GerritMihu/htl-loetregler-mini/3d/griffstück/griffstück_unten_v0.0.4.stl

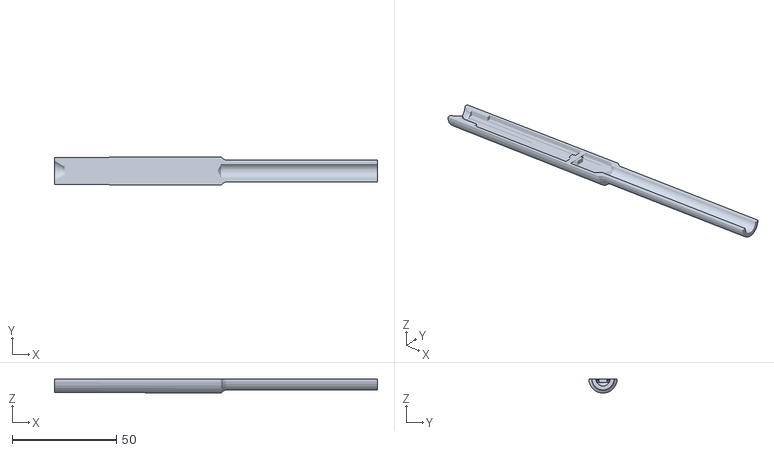
[picture p18: CAD file, 2024-12-23]
3d/griffstück/griffstück_unten_v0.0.4.stl
155.0 x 13.6 x 6.75
