GerritMihu/htl-loetregler-mini/3d/griffstück/griffstück_halbschale-rund_v2_Polycarbonat.3mf

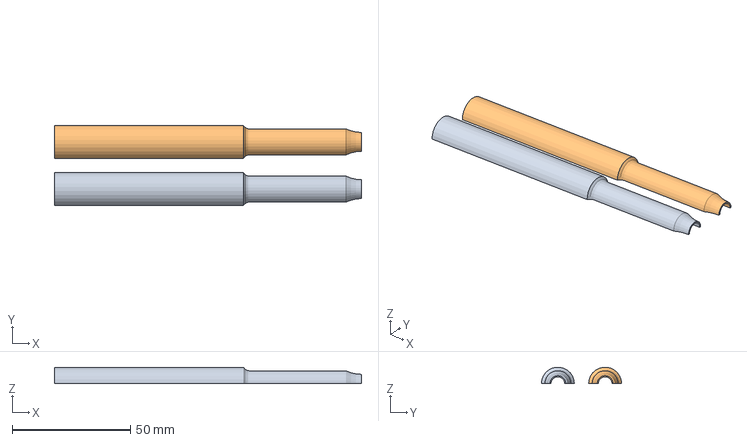
[picture p19: CAD file, 2024-12-23]
3d/griffstück/griffstück_halbschale-rund_v2_Polycarbonat.3mf
130.0 x 34.0 x 6.95 mm
