GerritMihu/htl-loetregler-mini/3d/griffstück/griffstück_v2_komplettset.3mf

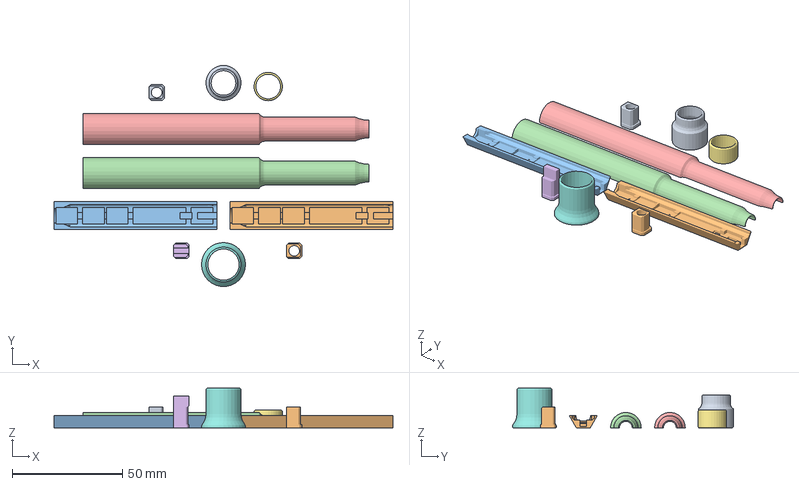
[picture p20: CAD file, 2024-12-23]
3d/griffstück/griffstück_v2_komplettset.3mf
154.0 x 100.5 x 18.0 mm
mittenring_v2.1.stl
griffstück_halbschale-hex_v2.stl
griffstück_halbschale-rund_v2.stl
griffstück_isolator_tc+.stl
endring_v2.1.stl
fingerkuppenring_v2.2.stl
griffstück_isolator_htc-_h+.stl
