GerritMihu/htl-loetregler-mini/3d/griffstück/griffstück_isolator_htc-_h+.stl

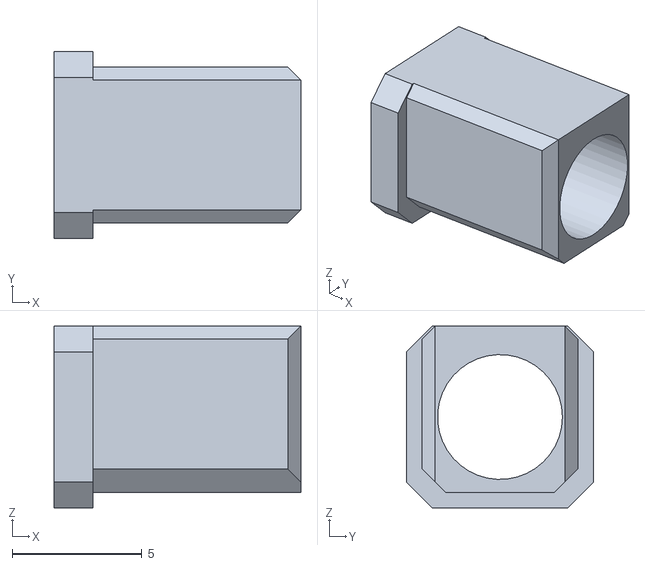
[picture p21: CAD file, 2024-12-23]
3d/griffstück/griffstück_isolator_htc-_h+.stl
9.50 x 7.20 x 7.00
