GerritMihu/htl-loetregler-mini/3d/griffstück/griffstück_oben_v0.0.1.3mf

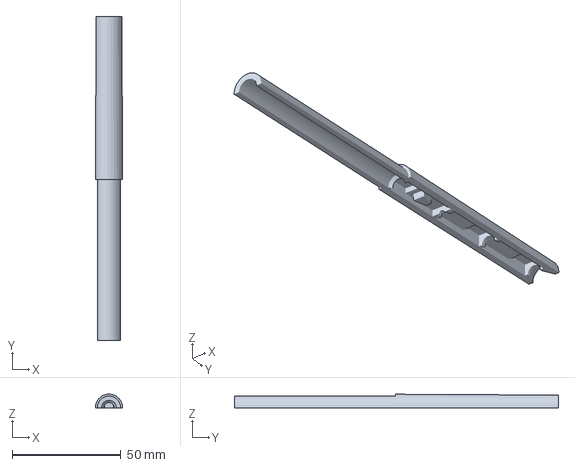
[picture p22: CAD file, 2024-12-23]
3d/griffstück/griffstück_oben_v0.0.1.3mf
12.6 x 149.0 x 6.25 mm
