GerritMihu/htl-loetregler-mini/3d/griffstück/fingerkuppenring_v2.3.stl

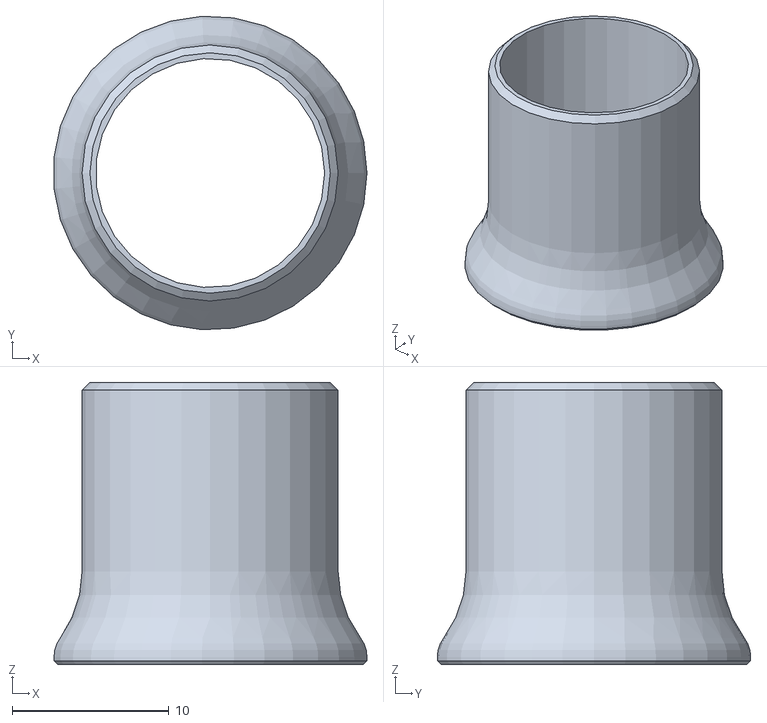
[picture p23: CAD file, 2024-12-23]
3d/griffstück/fingerkuppenring_v2.3.stl
19.9 x 20.0 x 18.0
