GerritMihu/htl-loetregler-mini/3d/griffstück/griffstück_unten_v0.0.1.3mf

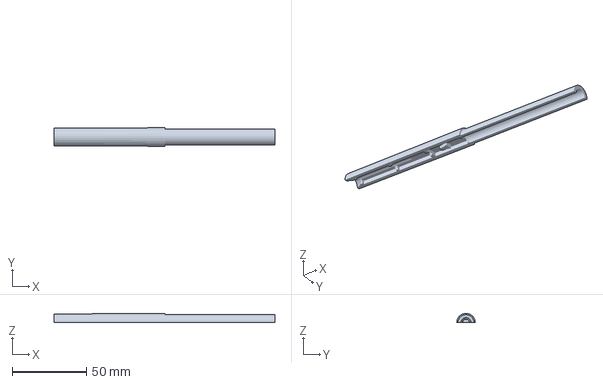
[picture p24: CAD file, 2024-12-23]
3d/griffstück/griffstück_unten_v0.0.1.3mf
149.0 x 12.6 x 6.25 mm
