GerritMihu/htl-loetregler-mini/3d/griffstück/federkontakt_v2.1_laser.dxf

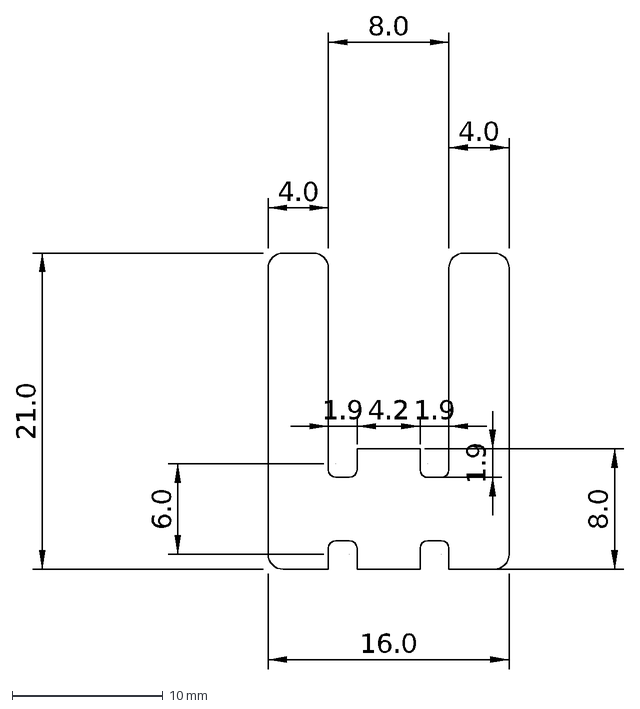
[picture p25: CAD file, 2024-12-23]
3d/griffstück/federkontakt_v2.1_laser.dxf
16.0
8.0
4.0
6.0
21.0
4.2
1.9
