GerritMihu/htl-loetregler-mini/3d/griffstück/griffstück_oben_v0.0.3.stl

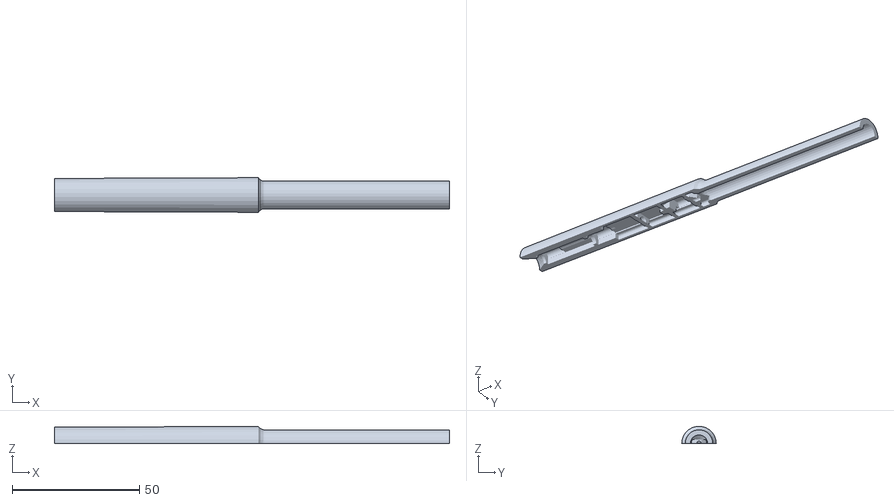
[picture p26: CAD file, 2024-12-23]
3d/griffstück/griffstück_oben_v0.0.3.stl
155.0 x 13.6 x 6.75
