GerritMihu/htl-loetregler-mini/3d/griffstück/griffstück_isolatoren_v2.2 Polycarbonat.3mf

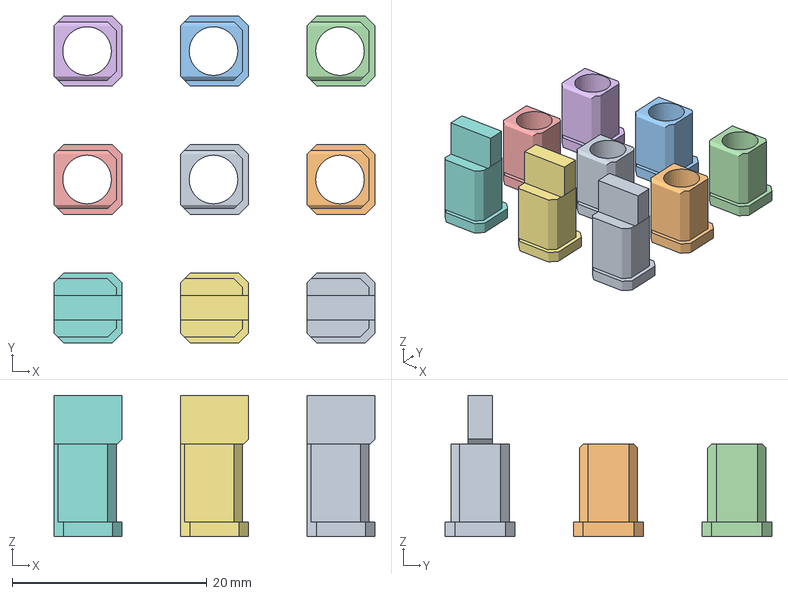
[picture p27: CAD file, 2024-12-23]
3d/griffstück/griffstück_isolatoren_v2.2 Polycarbonat.3mf
33.0 x 33.6 x 14.5 mm
griffstück_isolator_htc-_h+_v2.2.stl
griffstück_isolator_tc+.stl
