GerritMihu/htl-loetregler-mini/3d/griffstück/griffstück_halbschale-rund_v2.stl

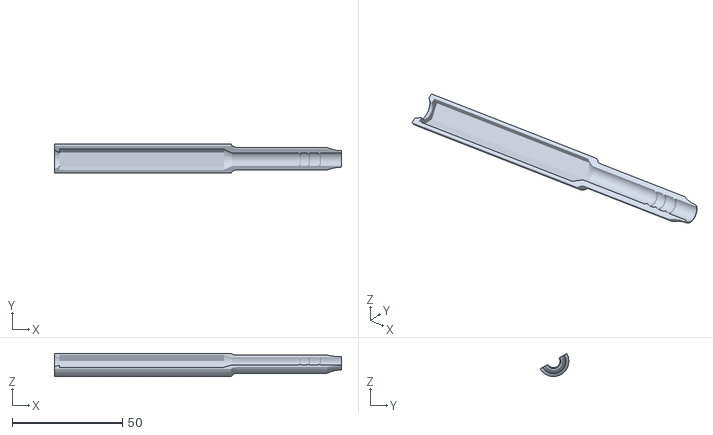
[picture p28: CAD file, 2024-12-23]
3d/griffstück/griffstück_halbschale-rund_v2.stl
130.0 x 13.1 x 10.5
